mstrupp/Stadion-Anzeigetafel/Nucleo-Code/Core/Inc/LEDMatrix.h

/*
 * LEDMatrix.h
 *
 *  Created on: Sep 23, 2021
 *      Author: michaelstrupp
 */

#ifndef INC_LEDMATRIX_H_
#define INC_LEDMATRIX_H_

#include "stm32g0xx_hal.h"

#include "Character.h"
#include "LED.h"

typedef struct {
	uint32_t numLEDs;
	uint8_t numCols;
	LED* leds;
	LED* ledsBuffer;

	TIM_HandleTypeDef* htim;
	uint32_t timerChannel;

	int isSending;

	// Intern variables
	int cursorPos;
	char alignment;
	int showRequest;
	// DMA
	uint32_t pwmBuffer[48];
	uint32_t nextLED;
} LEDMatrix;

void LEDMatrixInit(LEDMatrix* ledMatrix, uint32_t numLEDs, uint8_t numCols, TIM_HandleTypeDef* htim, uint32_t timerChannel);

// Sets the alignment of the text on the matrix.
// Existing text will not be aligned.
// char alignment must be 'l' (left), 'c' (center), 'r' (right) or 'a' (append to the right of the current position)
void LEDMatrixSetAlignment(LEDMatrix* ledMatrix, char alignment);

// Sets the cursor to the given position where 0 is the first column.
// Cursor position can be negative.
void LEDMatrixSetCursorPosition(LEDMatrix* ledMatrix, int position);

// Matrix Manipulation
// Shuts all leds off
void LEDMatrixClear(LEDMatrix* ledMatrix);
// Set a character at the current cursor position in the given color.
// The cursor will not move.
void LEDMatrixSetCharacter(LEDMatrix* ledMatrix, const Character* character, Color color);
// Adds a string to the end of the matrix in the given color
void LEDMatrixAddText(LEDMatrix* ledMatrix, char text[], Color color);

// Send the bit signals for the current LED configuration.
void LEDMatrixShow(LEDMatrix* ledMatrix);

// DMA Callback functions
// Fill the buffer with the next duty cycle values depending on the LED colors.
// The functions need to be called when the buffer is half/completely transferred.
// Call LEDMatrixBufferHalfSentCallback in HAL_TIM_PWM_PulseFinishedHalfCpltCallback.
// Call LEDMatrixBufferSentCallback in HAL_TIM_PWM_PulseFinishedCallback.

void LEDMatrixBufferHalfSentCallback(LEDMatrix* ledMatrix);
void LEDMatrixBufferSentCallback(LEDMatrix* ledMatrix);

// The width of a given text in pixels
int pixelWidth(const char text[]);

#endif /* INC_LEDMATRIX_H_ */
